benpeart/MarbleMadness/src/settings.cpp

#include "settings.h"
#include "debug.h"
#include "modes.h"
#include "render.h"
#include "RealTimeClock.h"

// -- EEPROM
Preferences preferences;
#define PREF_VERSION 1 // if setting structure has been changed, increment this number to reset all settings
#define PREF_NAMESPACE "pref"
#define PREF_KEY_VERSION "ver"

// A copy of what is stored in EEPROM so we can compare and only write out changes
marblemadness_settings EEPROMSettings;

// global settings anyone can read/write
marblemadness_settings settings;

// load persisted settings
void settingsSetup()
{
    // Init EEPROM, if not done before
    preferences.begin(PREF_NAMESPACE, false); // false = RW-mode
    if (preferences.getUInt(PREF_KEY_VERSION, 0) != PREF_VERSION)
    {
        preferences.clear(); // Remove all preferences under the opened namespace
        preferences.putUInt(PREF_KEY_VERSION, PREF_VERSION);
        DB_PRINTF("EEPROM init complete, all preferences deleted, new pref_version: %d\n", PREF_VERSION);
    }

    // load our settings from persistent storage
    EEPROMSettings.brightness = preferences.getInt("brightness", MAX_BRIGHTNESS);
    EEPROMSettings.speed = preferences.getInt("speed", MIN_SPEED);
    EEPROMSettings.mode = preferences.getInt("mode", 0);
#ifdef TIME
    EEPROMSettings.clockFace = preferences.getInt("clockFace", 0);
    EEPROMSettings.clockColor = CRGB::White;
    preferences.getBytes("clockColor", &EEPROMSettings.clockColor, sizeof(EEPROMSettings.clockColor));
#endif // TIME

    // copy the persisted settings to the current settings
    settings = EEPROMSettings;
};

// persist any changes to the settings
void settingsPersist()
{
    // if any changes have been made and not persisted, write them out now
    if (EEPROMSettings.brightness != settings.brightness)
    {
        EEPROMSettings.brightness = settings.brightness;
        preferences.putInt("brightness", EEPROMSettings.brightness);
        DB_PRINTF("settingsPersist: brightness = %d\r\n", EEPROMSettings.brightness);
    }
    if (EEPROMSettings.speed != settings.speed)
    {
        EEPROMSettings.speed = settings.speed;
        preferences.putInt("speed", EEPROMSettings.speed);
        DB_PRINTF("settingsPersist: speed = %d\r\n", EEPROMSettings.speed);
    }
    if (EEPROMSettings.mode != settings.mode)
    {
        EEPROMSettings.mode = settings.mode;
        preferences.putInt("mode", EEPROMSettings.mode);
        DB_PRINTF("settingsPersist: mode = %s\r\n", getMarbleMadnessMode(EEPROMSettings.mode));
    }
#ifdef TIME
    if (EEPROMSettings.clockFace != settings.clockFace)
    {
        EEPROMSettings.clockFace = settings.clockFace;
        preferences.putInt("clockFace", EEPROMSettings.clockFace);
        DB_PRINTF("settingsPersist: clockFace = %s\r\n", getClockFace(EEPROMSettings.clockFace));
    }
    if (EEPROMSettings.clockColor != settings.clockColor)
    {
        EEPROMSettings.clockColor = settings.clockColor;
        preferences.putBytes("clockColor", &EEPROMSettings.clockColor, sizeof(EEPROMSettings.clockColor));
        DB_PRINTF("settingsPersist: clockColor = #%06X\r\n", EEPROMSettings.clockColor.r << 16 | EEPROMSettings.clockColor.g << 8 | EEPROMSettings.clockColor.b);
    }
#endif // TIME
};
